GEROMSTUDIO/dmx-sans-fils/Shéma/Schematic_DMX-sans-fils-récepteur-V.4.0.png

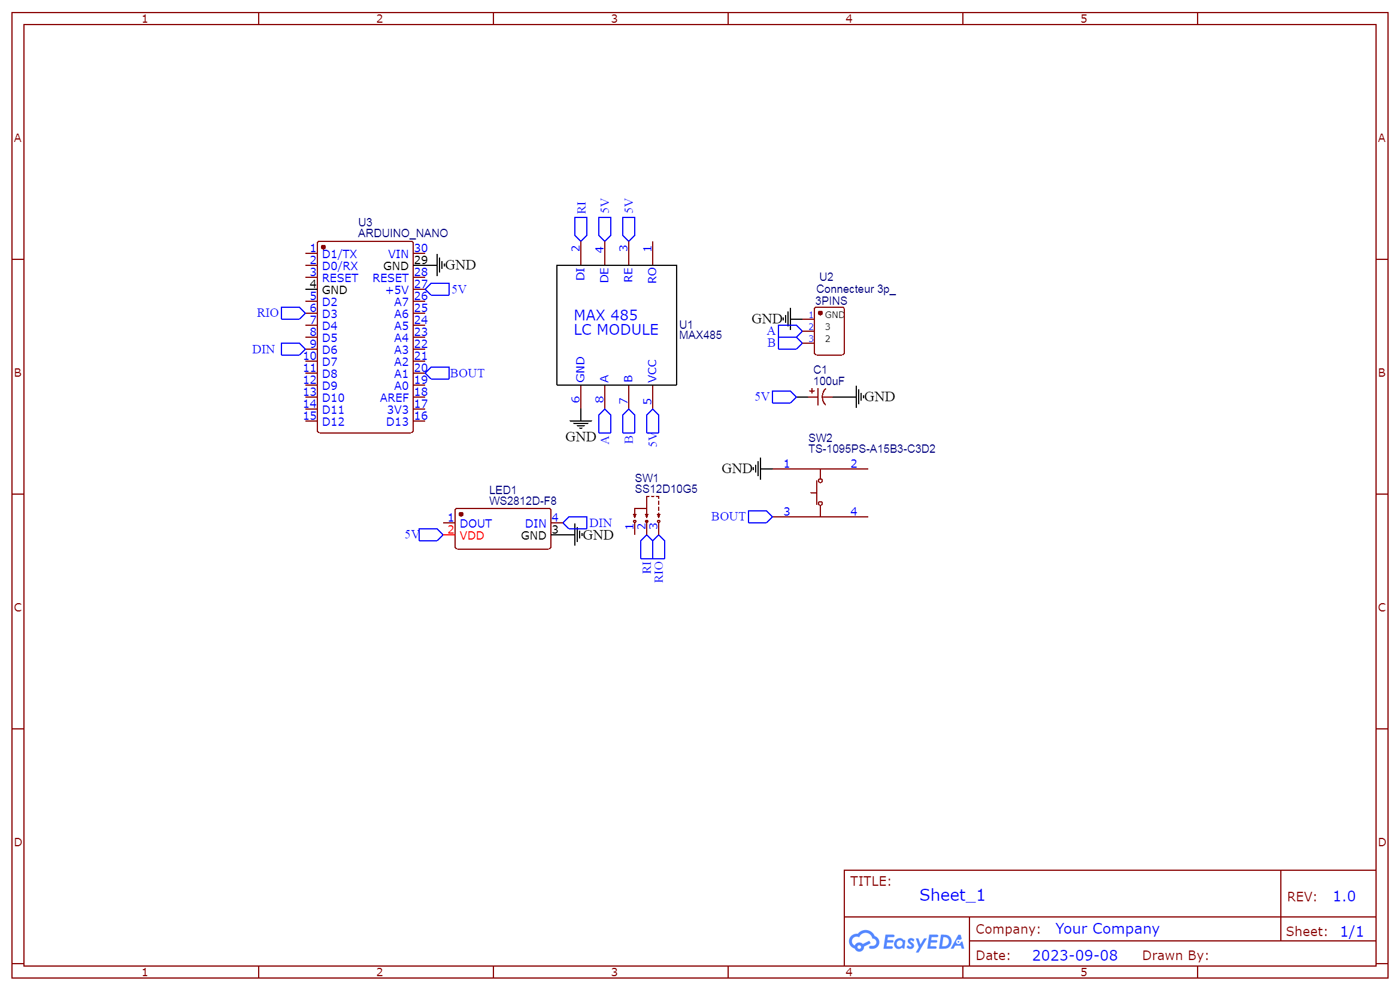
Shéma/Schematic_DMX-sans-fils-récepteur-V.4.0.png
